martinwoodward/PumpkinPi/images/multi-coloured-pumpkins.jpg

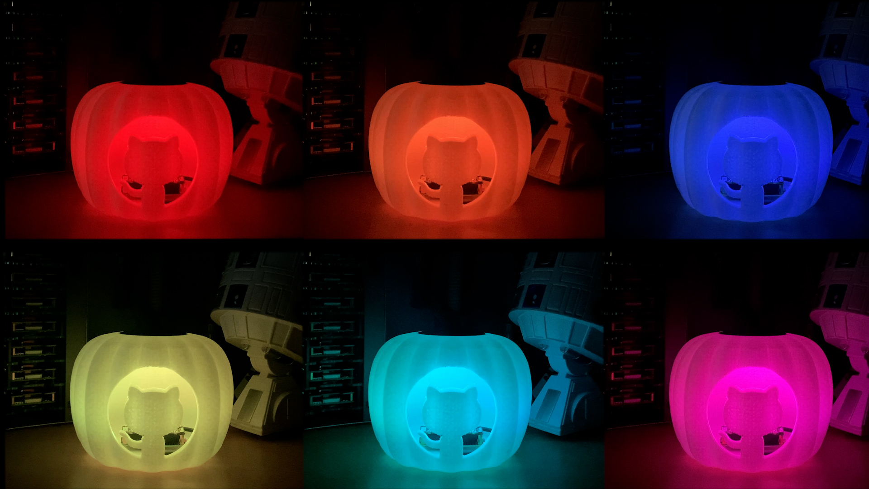
images/multi-coloured-pumpkins.jpg
