martinwoodward/PumpkinPi/images/pumpkin-white.jpg

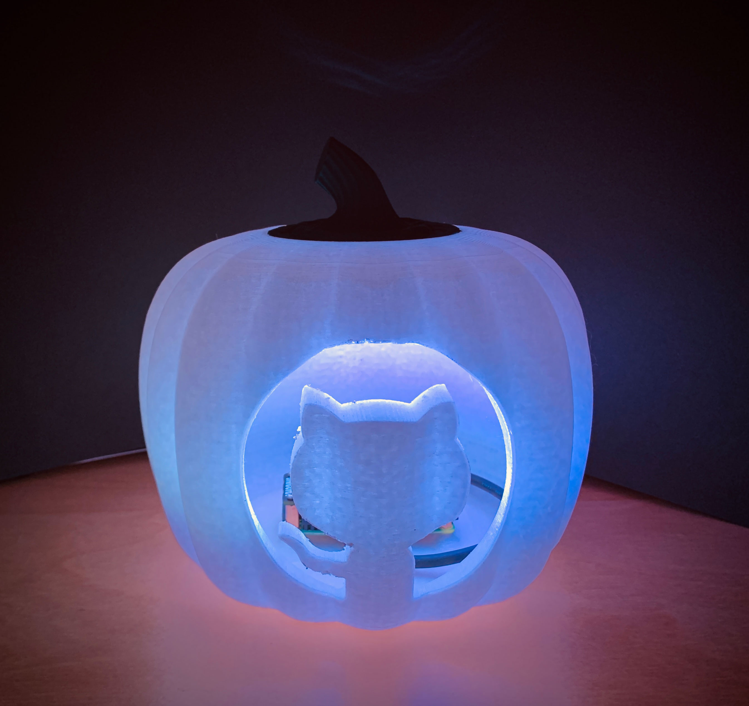
images/pumpkin-white.jpg
