martinwoodward/PumpkinPi/images/pumpkinpi-render-top.jpg

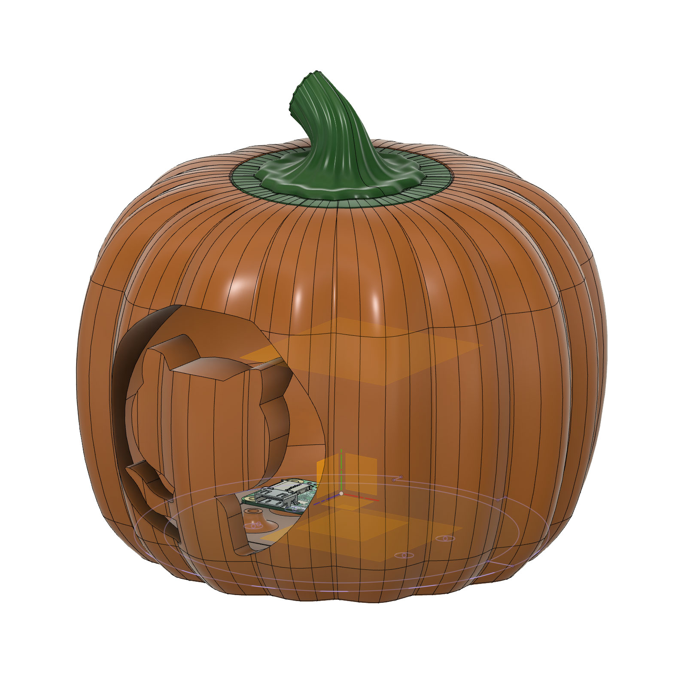
images/pumpkinpi-render-top.jpg
