martinwoodward/PumpkinPi/images/phat-install.jpg

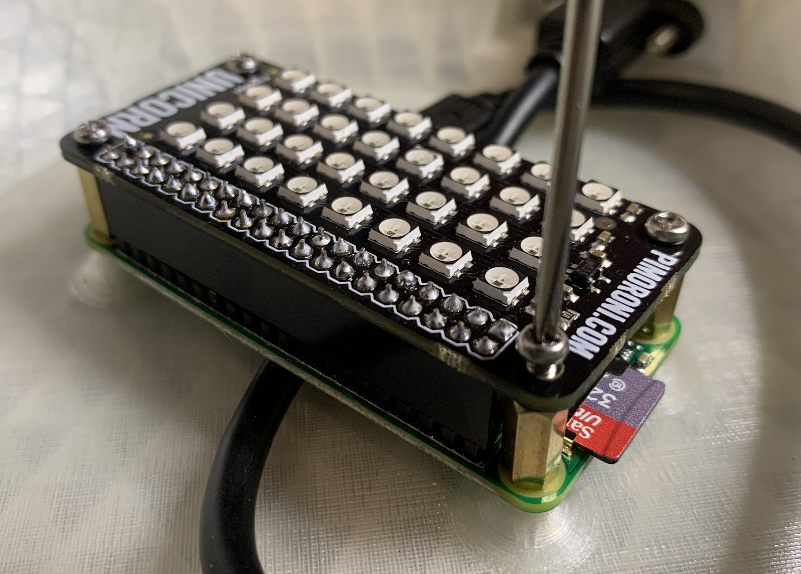
images/phat-install.jpg
